chriswernst/reflow-oven/images/ relay_wiring.jpg

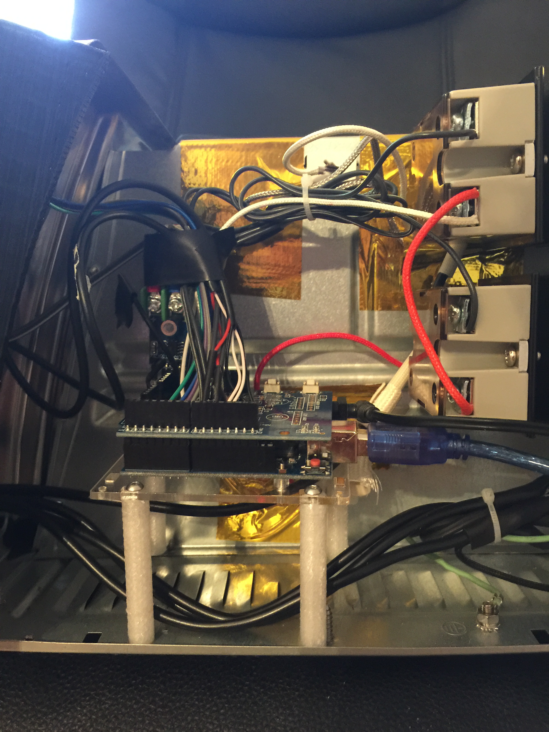
images/ relay_wiring.jpg
