chriswernst/reflow-oven/images/arduino_wiring.jpg

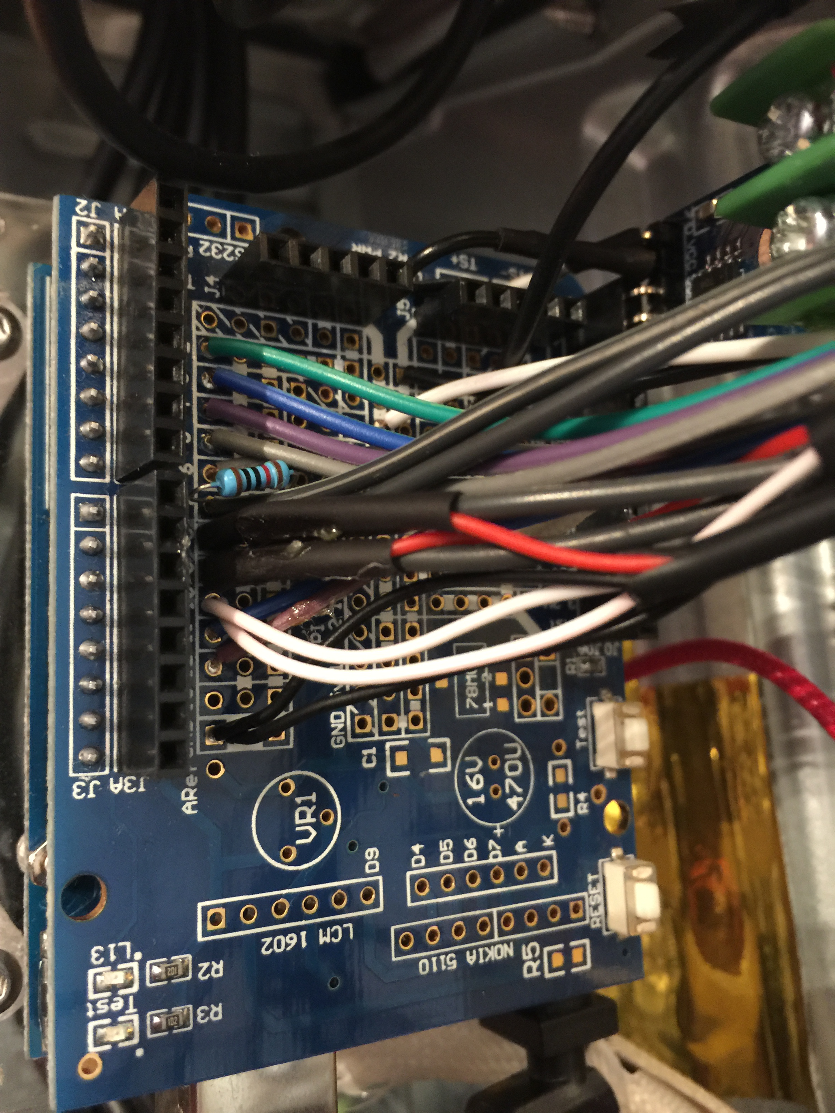
images/arduino_wiring.jpg
